TinyCircuits/TinyCircuits-TinyShield-433MHz_Radio_SI4432-ASD2162/images/ASD2162-R-Tutorial-Image-01.jpg

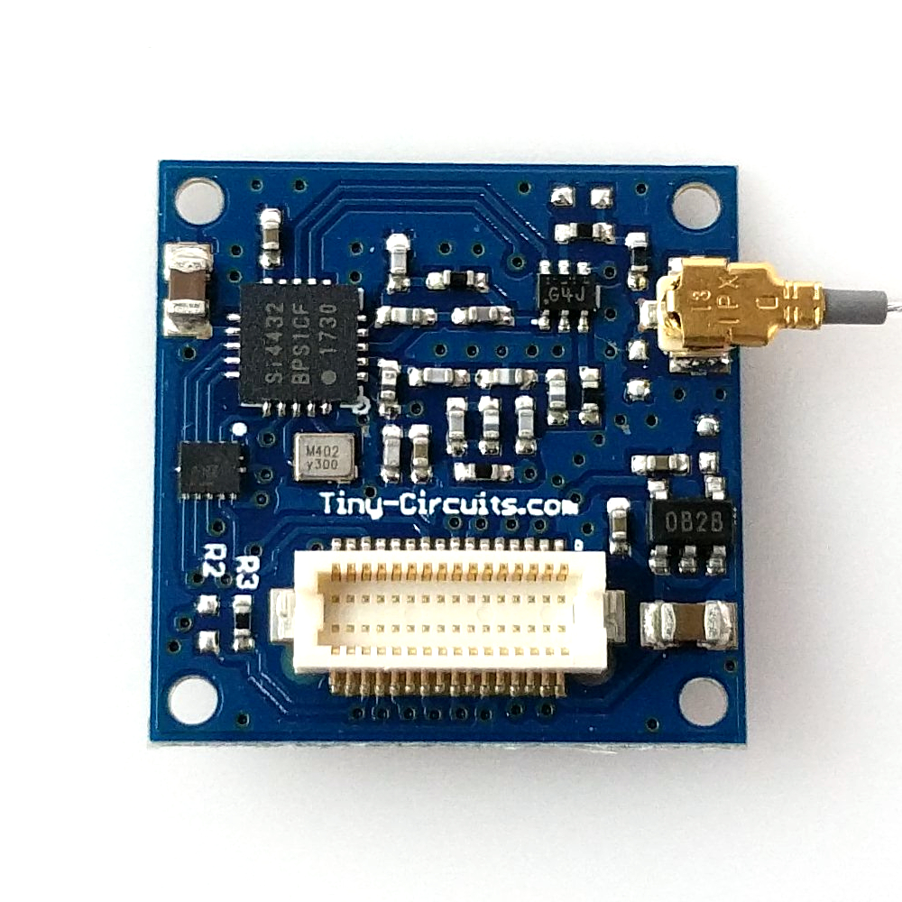
images/ASD2162-R-Tutorial-Image-01.jpg
