TinyCircuits/TinyCircuits-TinyShield-433MHz_Radio_SI4432-ASD2162/examples/433_transmitter/MotorDriver/MotorDriver.cpp

/*
MotorDriver.cpp - Last modified 11 July 2018

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
Written by Ben Rose for TinyCircuits.

The latest version of this library can be found at https://tinycircuits.com/
*/

#include "MotorDriver.h"
#include <inttypes.h>
#include "Arduino.h"
#include "Wire.h"

#define _BV(bit) (1 << (bit)) 

MotorDriver::MotorDriver(uint8_t addr)
{
  address = T841_ADDRESS+addr;
}

uint8_t MotorDriver::begin(uint16_t PWMperiod)
{
  writeByte(COMMAND_SET_MODE,MODE_REGISTER_DEC);//write to the T841 registers directly
  if(read(FIRMWARE_REVISION_REG)!=EXPECTED_SERVO_FIRMWARE && read(FIRMWARE_REVISION_REG)!=EXPECTED_MOTOR_FIRMWARE)
    return 1;
  writeByte(T841_DDRA, _BV(7)|_BV(2)|_BV(1));
  writeByte(T841_DDRB, _BV(2));
  writeByte(T841_TOCPMSA1, _BV(T841_TOCC7S1)|_BV(T841_TOCC6S1));
  writeByte(T841_TOCPMSA0, _BV(T841_TOCC1S0)|_BV(T841_TOCC0S0));
  writeByte(T841_TCCR1A, _BV(T841_COM0A1)|_BV(T841_COM0B1)|_BV(T841_WGM11));
  writeByte(T841_TCCR2A, _BV(T841_COM2A1)|_BV(T841_COM0B1)|_BV(T841_WGM21));
  writeByte(T841_TCCR1B, _BV(T841_WGM13)|_BV(T841_WGM12)|_BV(T841_CS10));
  writeByte(T841_TCCR2B, _BV(T841_WGM23)|_BV(T841_WGM22)|_BV(T841_CS20));
  writeByte(COMMAND_SET_MODE, MODE_COMMAND);//send interpreted commands- see header file
  writeByte(COMMAND_CLOCK_PRESCALER, T841_CLOCK_PRESCALER_1);
  writeByte(COMMAND_PRESCALER_1, T841_TIMER_PRESCALER_8);//This default changed from T841_TIMER_PRESCALER_1 July 11 2018 to suit the servo driver
  writeByte(COMMAND_PRESCALER_2, T841_TIMER_PRESCALER_8);//This default changed from T841_TIMER_PRESCALER_1 July 11 2018 to suit the servo driver
  writeCommand(COMMAND_TIMER_1, PWMperiod);
  writeCommand(COMMAND_TIMER_2, PWMperiod);
  writeByte(COMMAND_SET_FAILSAFE_PRESCALER, T841_TIMER_PRESCALER_8);
  return 0;
}

void MotorDriver::writeByte(uint8_t b1){
  Wire.beginTransmission(address);
  Wire.write(b1);
  Wire.endTransmission();
}
  
void MotorDriver::writeByte(uint8_t b1,uint8_t b2){
  Wire.beginTransmission(address);
  Wire.write(b1);
  Wire.write(b2);
  Wire.endTransmission();
}

void MotorDriver::writeByte(uint8_t b1,uint8_t b2,uint8_t b3){
  Wire.beginTransmission(address);
  Wire.write(b1);
  Wire.write(b2);
  Wire.write(b3);
  Wire.endTransmission();
}  

void MotorDriver::writeCommand(uint8_t cmd, uint16_t val){
  int MSB=val>>8;
  Wire.beginTransmission(address);
  Wire.write(cmd);
  Wire.write(val);
  Wire.write(MSB);
  Wire.endTransmission();
  
}

void MotorDriver::writeCommand(uint8_t cmd, uint16_t val1, uint16_t val2){
  int MSB=val1>>8;
  Wire.beginTransmission(address);
  Wire.write(cmd);
  Wire.write(val1);
  Wire.write(MSB);
  MSB=val2>>8;
  Wire.write(val2);
  Wire.write(MSB);
  Wire.endTransmission();
  
}

void MotorDriver::writeCommand(uint8_t cmd, uint16_t val1, uint16_t val2, uint16_t val3, uint16_t val4){
  int MSB=val1>>8;
  Wire.beginTransmission(address);
  Wire.write(cmd);
  Wire.write(val1);
  Wire.write(MSB);
  MSB=val2>>8;
  Wire.write(val2);
  Wire.write(MSB);
  MSB=val3>>8;
  Wire.write(val3);
  Wire.write(MSB);
  MSB=val4>>8;
  Wire.write(val4);
  Wire.write(MSB);
  Wire.endTransmission();
}


uint8_t MotorDriver::read(uint8_t reg){
  writeByte(reg);
  Wire.requestFrom(address,(uint8_t)1);
  return Wire.read();
}

void MotorDriver::setFailsafe(uint16_t ms){
  if(ms>0x3FFF)ms=0x3FFF;
  writeCommand(COMMAND_SET_FAILSAFE_TIMEOUT, ms*4);//using defualt settings- really ~1.024ms
}

void MotorDriver::setMotor(uint8_t motor, int16_t val){
  if(motor==1){
    if(val>0){
      writeCommand(COMMAND_MOTOR_1,0,abs(val));
    }else{
      writeCommand(COMMAND_MOTOR_1,abs(val),0);
    }
  }else if(motor==2){
    if(val>0){
      writeCommand(COMMAND_MOTOR_2,0,abs(val));
    }else{
      writeCommand(COMMAND_MOTOR_2,abs(val),0);
    }
  }
}


void MotorDriver::setServo(uint8_t servo, uint16_t val){
  if(servo>=1 && servo<=4){
    writeCommand(servo, val);
  }
}
